ian7aylor/ECE411Practicum/Logistics/Project_Preliminaries/Practicum_Project_Ideas.pdf

# Practicum

## Top Three Project Ideas

Portland State University

Maseeh College of Engineering & Computer Science

Department of Electrical & Computer Engineering

### Authors:

Nick Long

Marcus Chalona

Ali Saad

Ian Taylor

### October 12, 2019


ECE 411

Industry Design Processes

Lab 1 Report | PSU ECE 411

## Contents

1 Project Ideas | 2

1.3 Project Idea #3 - Dancing Lights (Sound Frequency to LED Visualizer) 4

2 Conclusion | 5
1900 SW 4th Ave,, Portland, OR 97201 • https://github.com/ECE411Practicum (https://github.com/ian7aylor/ECE411Practicum/) | 1

## 1 Project Ideas

### 1.1 Project Idea #1 - HVAC Controlled Fan for a Server

### Room

Description: A temperature sensor will take in temperature values and delivers this information to a microcontroller. This microcontroller will then use arithmetic to determine the amount of voltage that will go on the output. This output voltage will drive a fan.

Sensor: Temperature Sensor
Controller: ATMega32U4-AU
Actuator: Fan
1900 SW 4th Ave,, Portland, OR 97201 • https://github.com/ECE411Practicum (https://github.com/ian7aylor/ECE411Practicum/) | 2

### 1.2 Project Idea #2 - Solar Light Sensor

Description: A solar panel will induce current and charge a battery. The controller will check voltage values from the previous 15 minutes to determine whether or not to start a motor that will change the angle of the solar panel(s) to find the next optimal position.

Sensor: Solar Array
Controller: ATMega32U4-AU
Actuator: Motor for realignment of solar panel(s)
1900 SW 4th Ave,, Portland, OR 97201 • https://github.com/ECE411Practicum (https://github.com/ian7aylor/ECE411Practicum/) | 3

### 1.3 Project Idea #3 - Dancing Lights (Sound Frequency to

### LED Visualizer)

Description: A microphone will be connected to multiple bandpass filters with specific frequency ranges. These filters will be connected to input pins of the ATMega32U4-AU. The ATMega32U4-AU will be programmed to take the voltage input from the bandpass filters and determine which LED strips to light up on the Neopixel LED strip.

Sensor: Microphone
Controller: ATMega32U4-AU
Actuator: Neopixels
1900 SW 4th Ave,, Portland, OR 97201 • https://github.com/ECE411Practicum (https://github.com/ian7aylor/ECE411Practicum/) | 4

## 2 Conclusion

As a group, we have decided that the Dancing Lights (Sound Frequencies to LED Visualization) project will give us the right amount of challenge for a 10 week project. We have equal amount of electrical and computer engineering majors in the group, so it was essential to have both analog and digital components.

1900 SW 4th Ave,, Portland, OR 97201 • https://github.com/ECE411Practicum (https://github.com/ian7aylor/ECE411Practicum/) | 5
