ian7aylor/ECE411Practicum/Logistics/ECE411HW4_ProjectSchedule.pdf

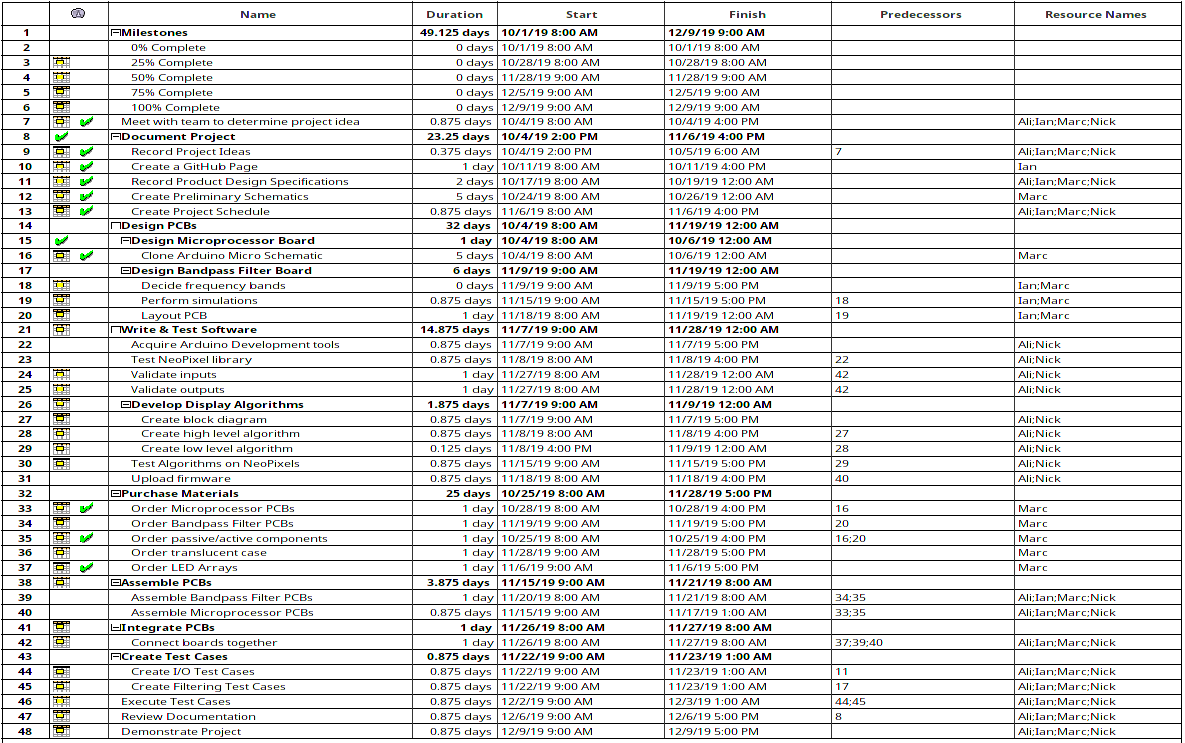
[picture p4: page 1]
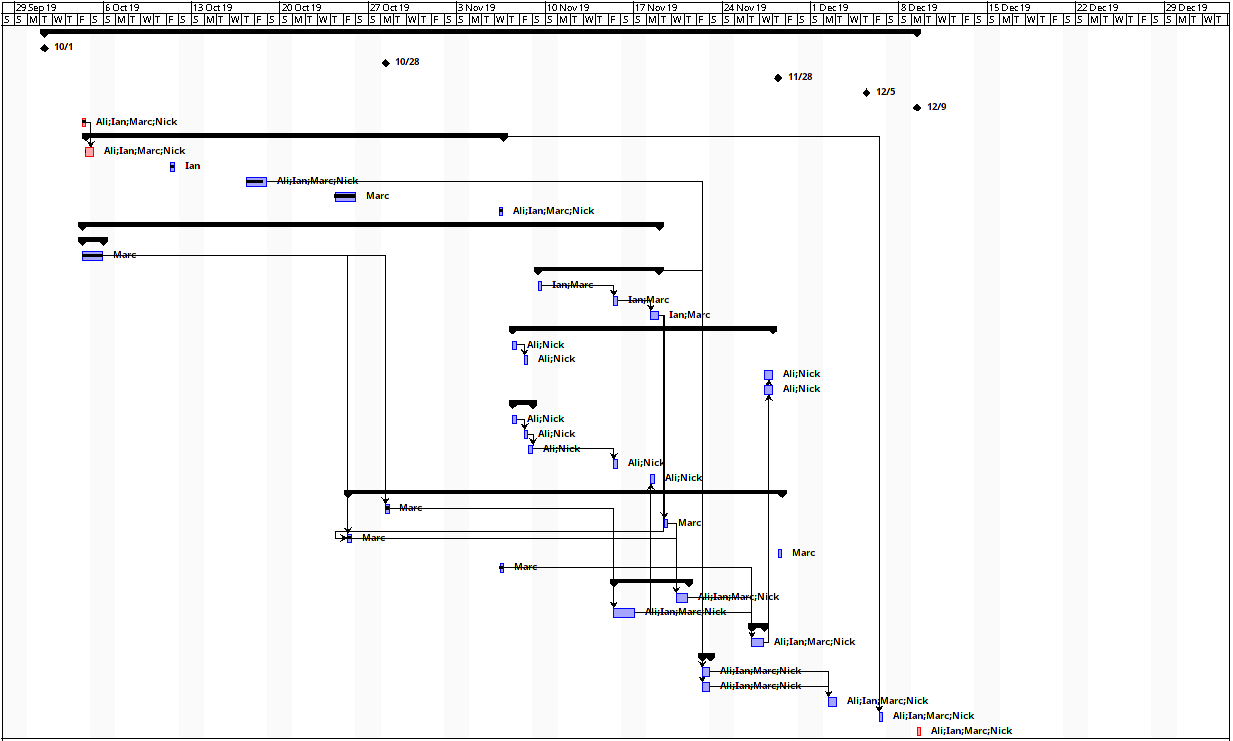
[picture p5: page 2]
