ian7aylor/ECE411Practicum/PCB Design & Layout/Layout/Ver1.2/PCB_Micro-Complete-Ver1.2_20191123182838/2adf127c-40fa-482e-ba70-ac2b44b57d2d.pdf

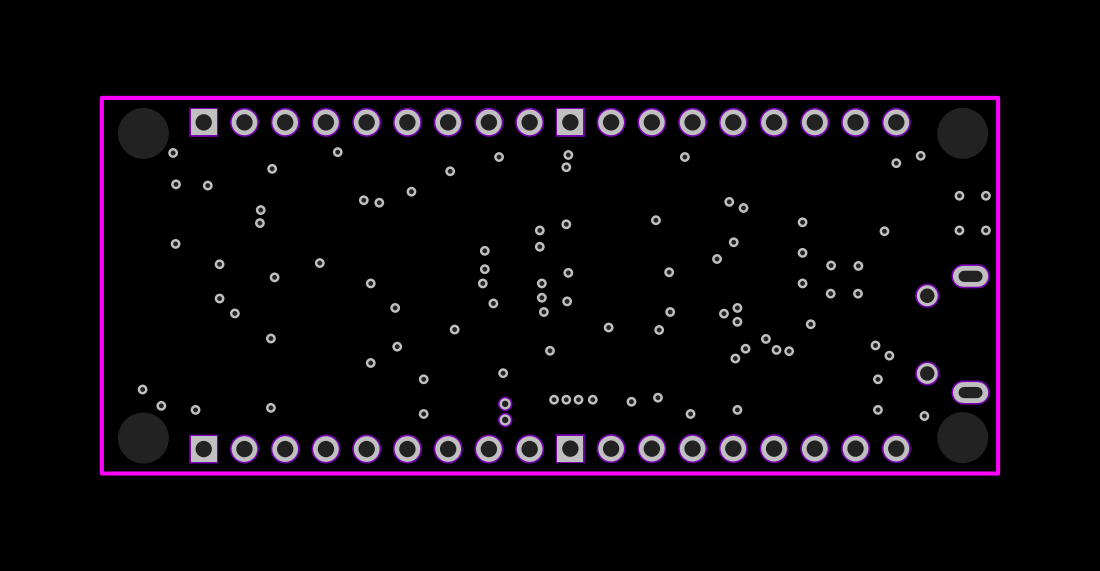
[picture p27: page 1]
