ian7aylor/ECE411Practicum/PCB Design & Layout/Layout/Ver1.2/PCB_Micro-Complete-Ver1.2_20191123182838/3e3d6713-1ce4-48b5-b2b1-c073c7c68c88.pdf

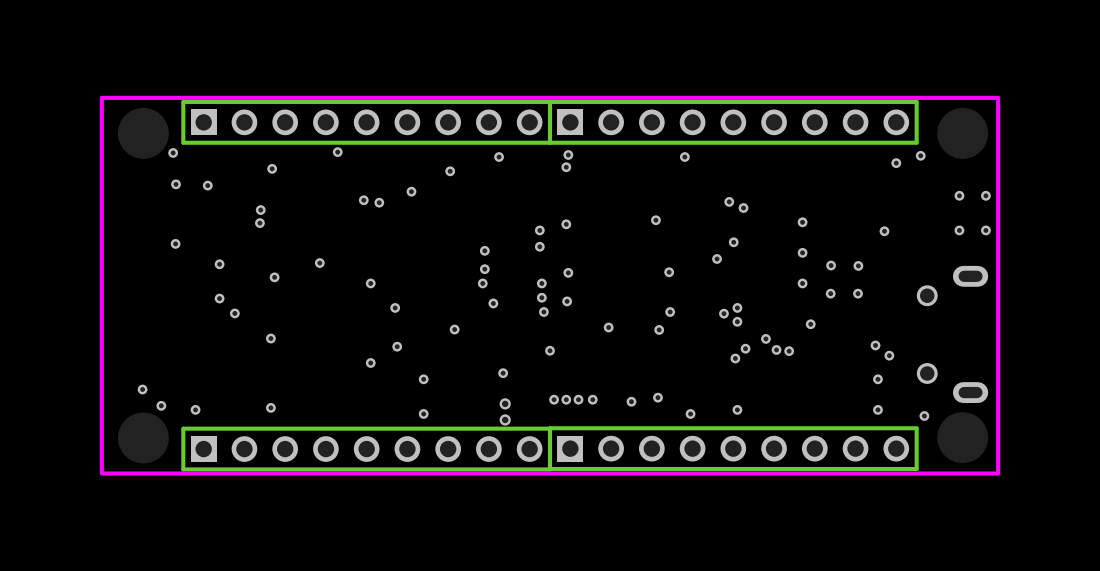
[picture p28: page 1]
