ian7aylor/ECE411Practicum/PCB Design & Layout/Layout/Ver1.2/PCB_Micro-Complete-Ver1.2_20191123182838/42185755-5dae-47f9-ac27-efa17913c4ca.pdf

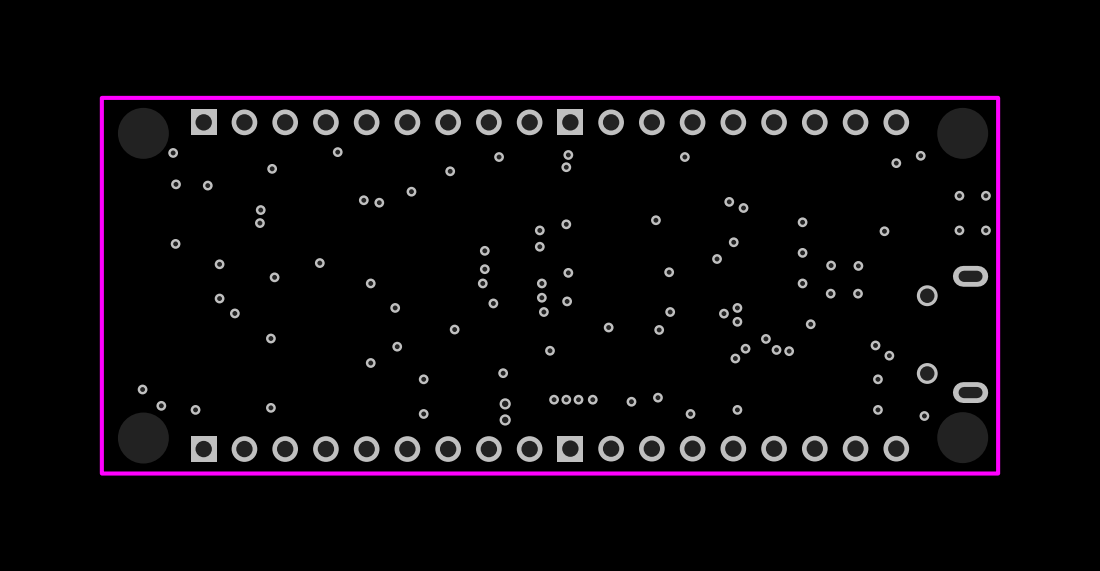
[picture p29: page 1]
