ian7aylor/ECE411Practicum/PCB Design & Layout/Layout/Ver1.2/PCB_Micro-Complete-Ver1.2_20191123182838/78972058-2b17-489f-846a-e816b7262c7a.pdf

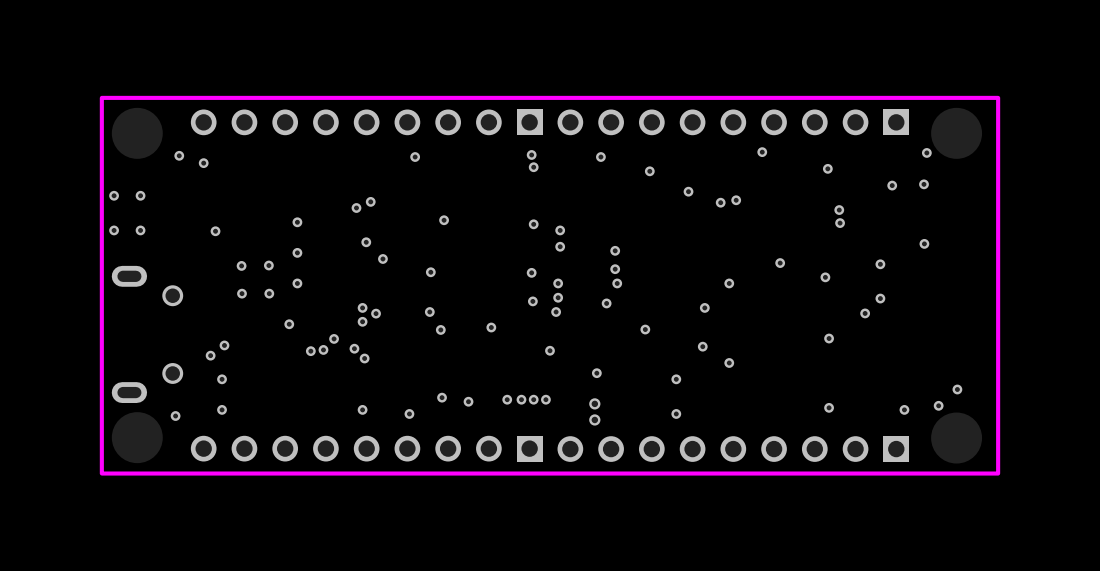
[picture p30: page 1]
