ian7aylor/ECE411Practicum/PCB Design & Layout/Layout/Ver1.2/PCB_Micro-Complete-Ver1.2_20191123182838/7be0d5c9-0151-4e07-a698-6b192da0d526.pdf

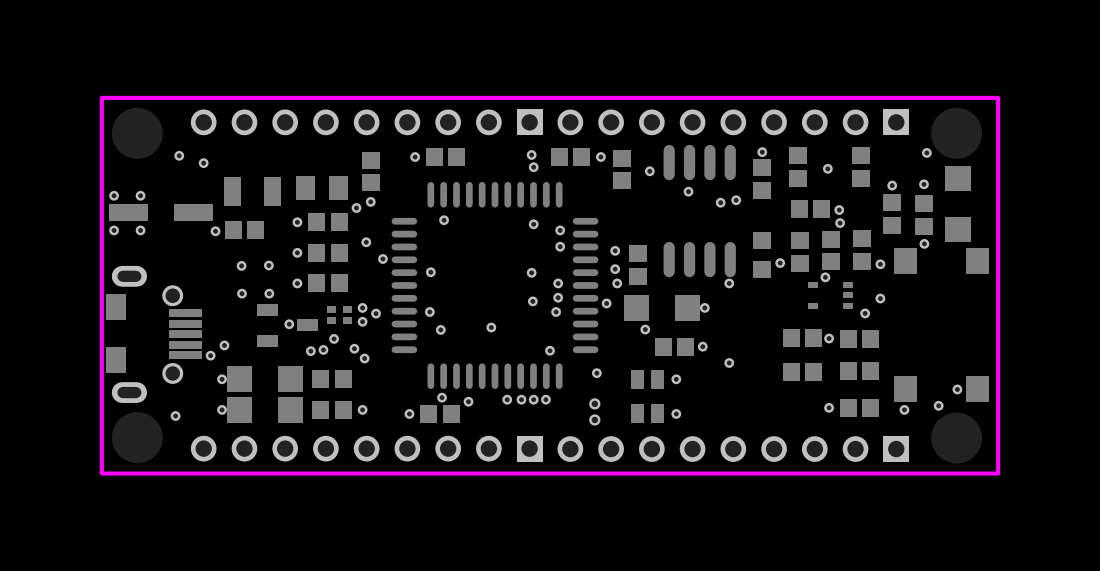
[picture p31: page 1]
