ian7aylor/ECE411Practicum/PCB Design & Layout/Layout/Ver1.2/PCB_Micro-Complete-Ver1.2_20191123182838/7daf5881-57eb-4031-89fc-7f53fe63a61d.pdf

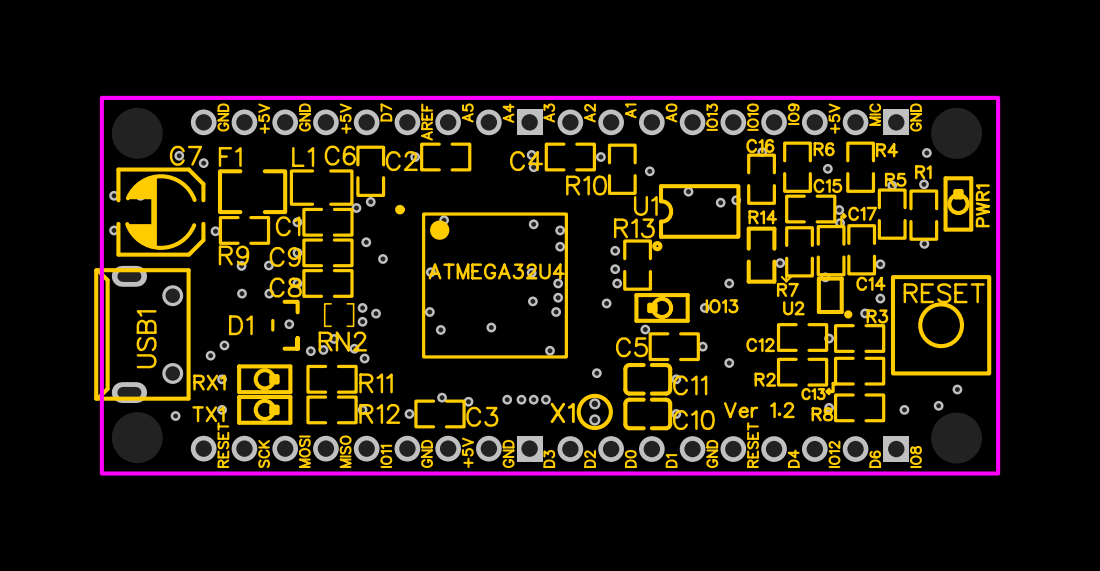
[picture p32: page 1]
