ian7aylor/ECE411Practicum/PCB Design & Layout/Layout/Ver1.2/PCB_Micro-Complete-Ver1.2_20191123182838/902dd1ad-2829-45e7-b100-44baf6f26a92.pdf

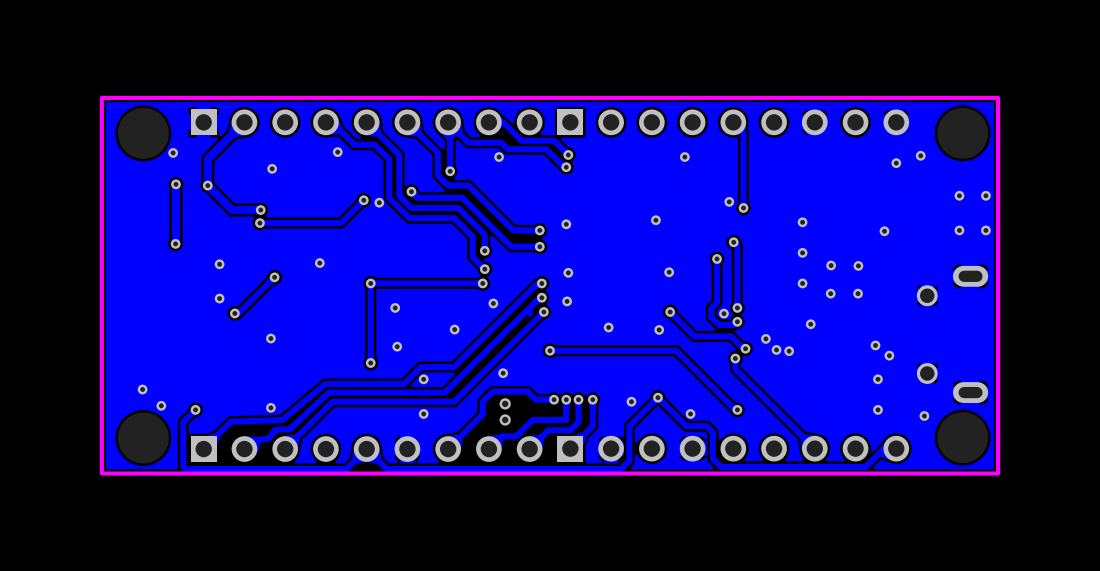
[picture p33: page 1]
