ian7aylor/ECE411Practicum/PCB Design & Layout/Layout/Ver1.2/PCB_Micro-Complete-Ver1.2_20191123182838/e6dc7ab0-4b18-48ef-a373-c5064e3a3ff5.pdf

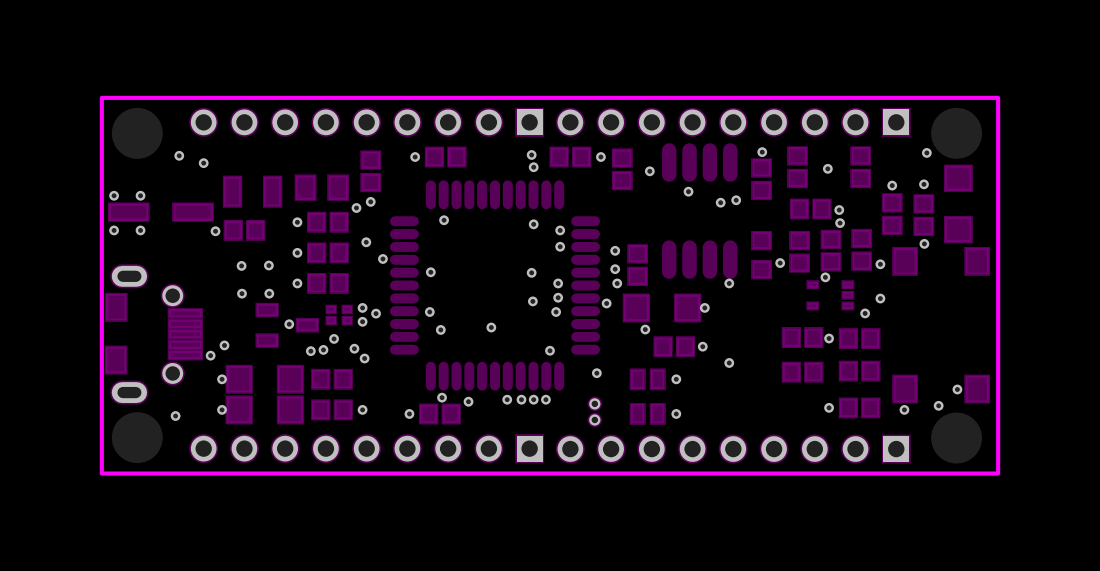
[picture p34: page 1]
