ian7aylor/ECE411Practicum/PCB Design & Layout/Layout/Ver1.2/PCB_Micro-Complete-Ver1.2_20191123183032/0f5fbee5-654c-4553-b34e-9a6330f1ae8d.pdf

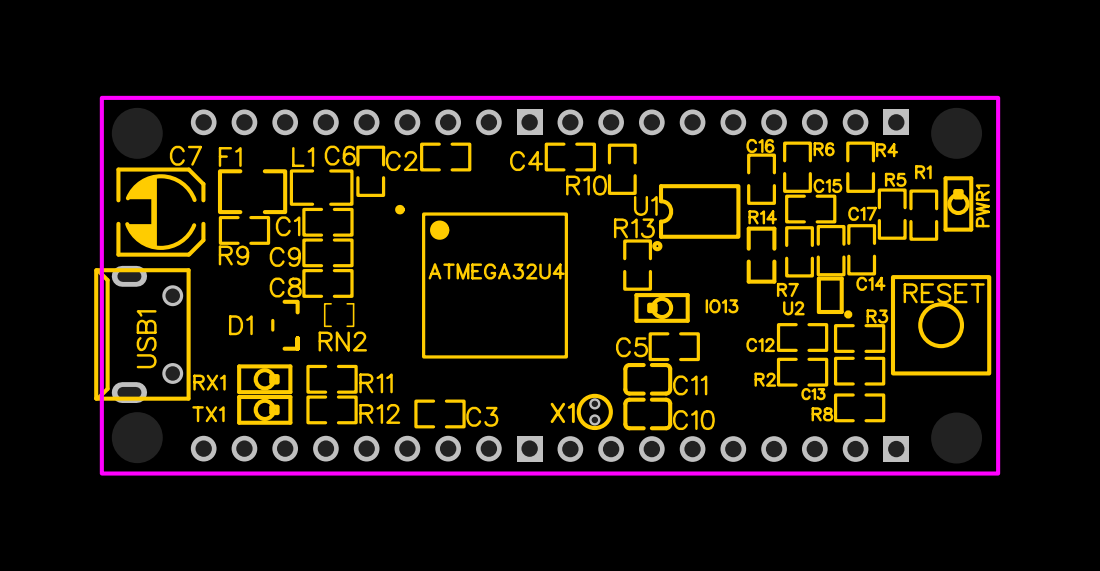
[picture p35: page 1]
