ian7aylor/ECE411Practicum/PCB Design & Layout/Layout/Ver1.2/PCB_Micro-Complete-Ver1.2_20191123183032/14120e1c-3400-4aa1-8a03-b37c3c2f251e.pdf

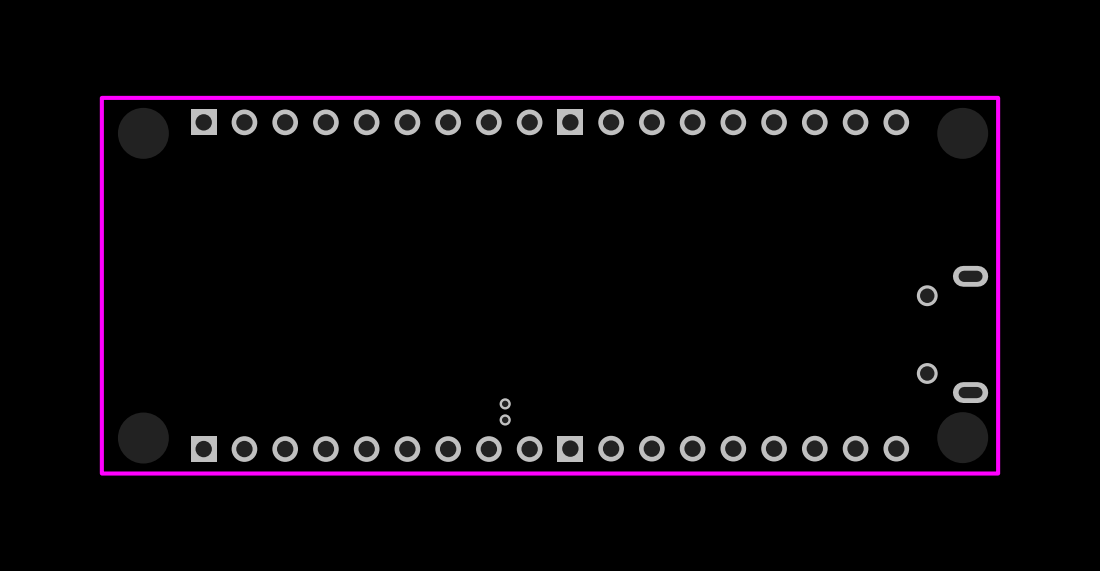
[picture p36: page 1]
