ian7aylor/ECE411Practicum/PCB Design & Layout/Layout/Ver1.2/PCB_Micro-Complete-Ver1.2_20191123183032/2fd0ea34-d89d-4401-8a14-ce33425fee76.pdf

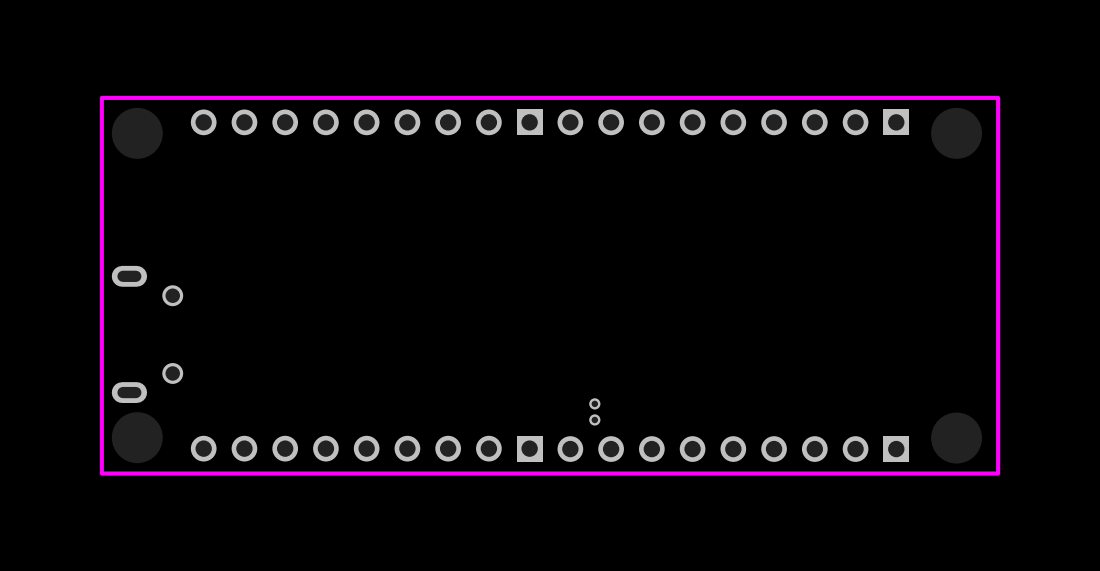
[picture p37: page 1]
