ian7aylor/ECE411Practicum/PCB Design & Layout/Layout/Ver1.2/PCB_Micro-Complete-Ver1.2_20191123183032/3119c9f1-c6d6-4f14-a6e9-f40058ee00e6.pdf

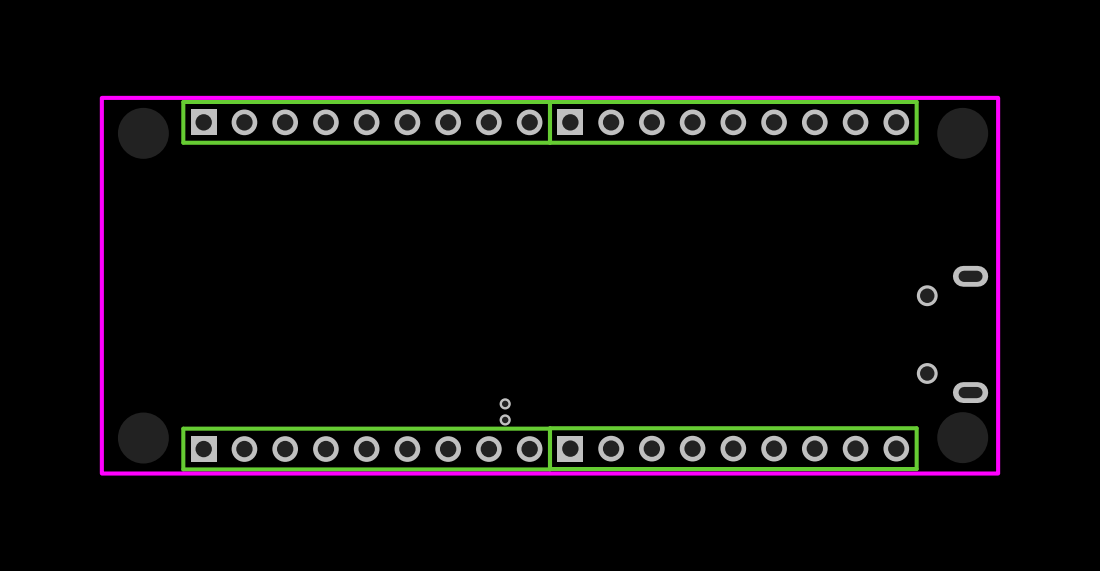
[picture p38: page 1]
