ian7aylor/ECE411Practicum/PCB Design & Layout/Layout/Ver1.2/PCB_Micro-Complete-Ver1.2_20191123183032/31f5569c-e1a5-4952-9578-0bfc36f0eb89.pdf

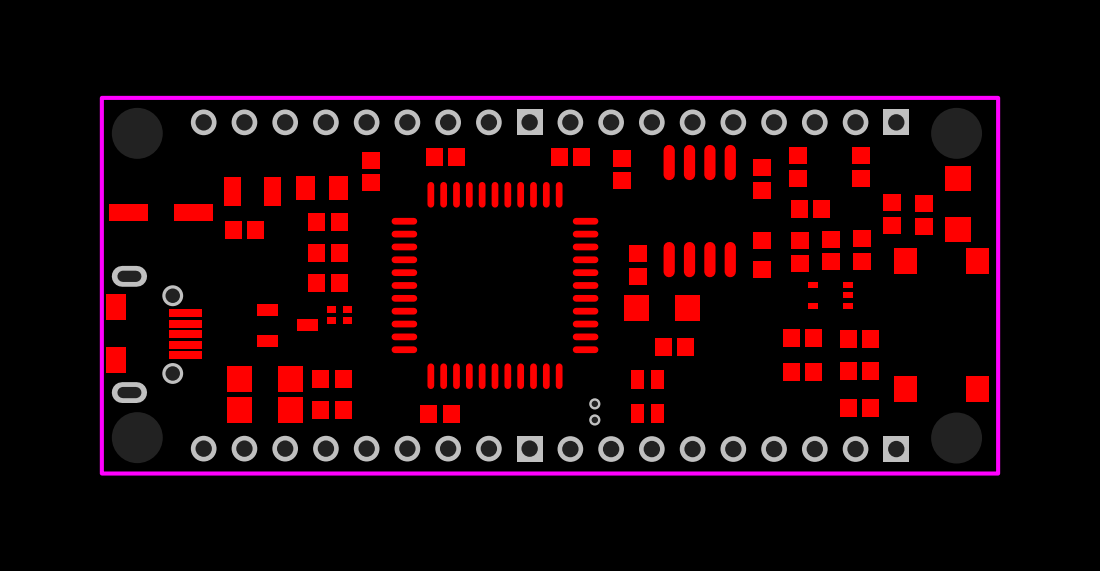
[picture p39: page 1]
