ian7aylor/ECE411Practicum/PCB Design & Layout/VER1.0/Schematic/Schematic_ECE411_ATMEGA32U4 Micro Ver1.0_20191204032329.pdf

## Analog Reference

+5V Selector | +5V Regulator

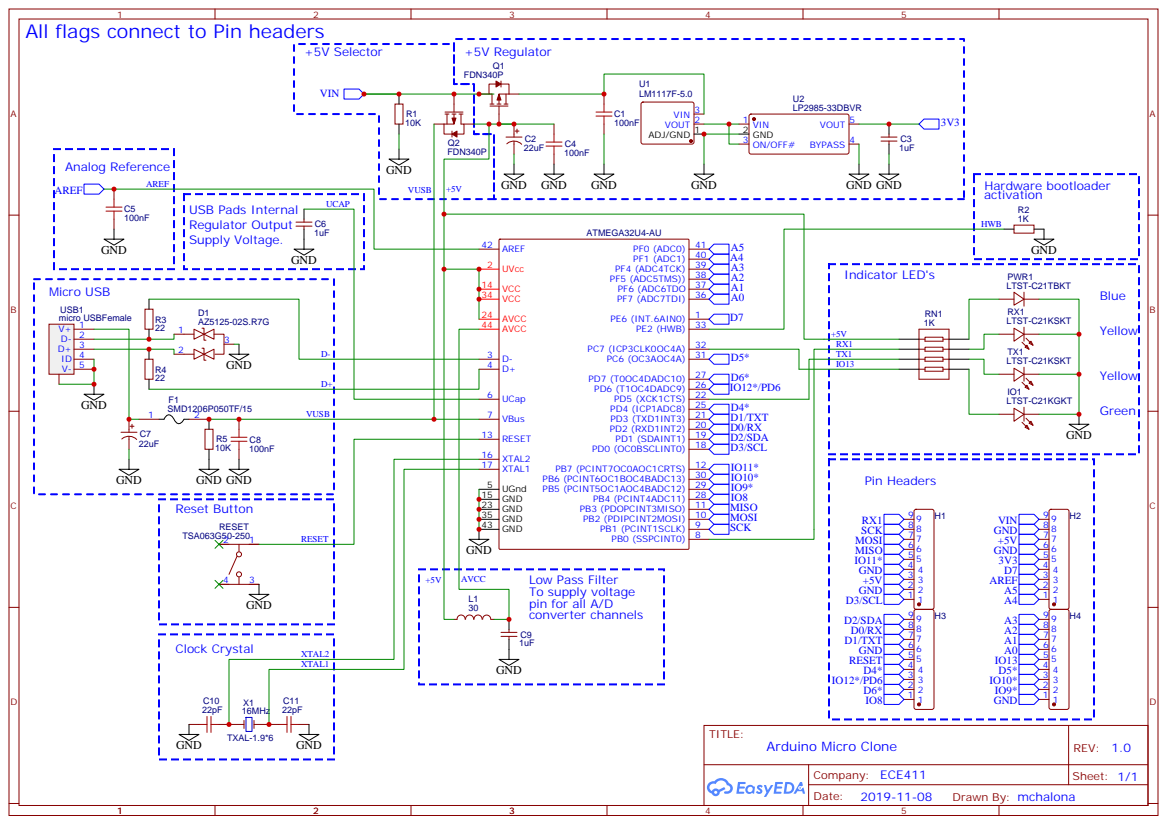
[picture p40: page 1]

All flags connect to Pin headers
