ian7aylor/ECE411Practicum/PCB Design & Layout/VER1.1/Schematic/Schematic_ECE411_ATMEGA32U4 Micro Ver1.1_20191204032943.pdf

## Analog Reference

## USB Pads Internal

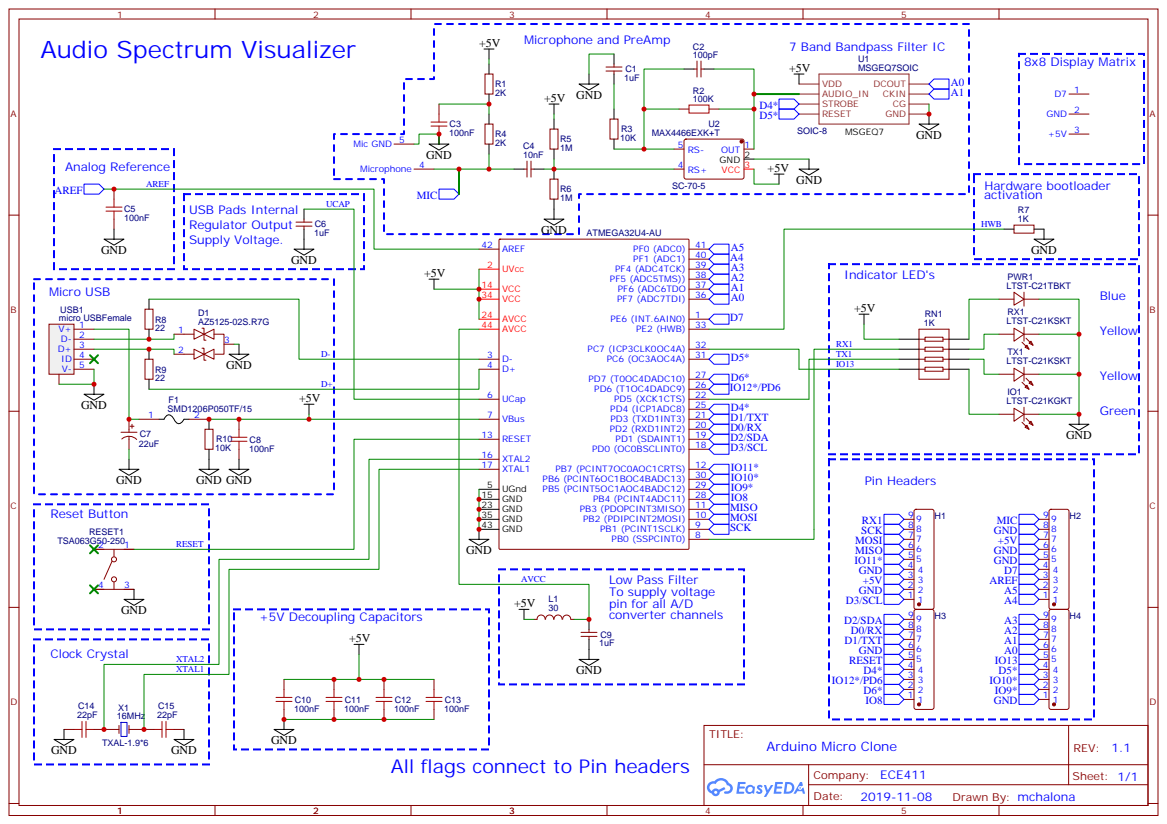
[picture p41: page 1]

7 Band Bandpass Filter IC Microphone and PreAmp

All flags connect to Pin headers
