ian7aylor/ECE411Practicum/PCB Design & Layout/Schematic/Ver1.0/Schematic_Practicum Project ECE411_20191030233733.pdf

## Analog Reference

+5V Selector | +5V Regulator

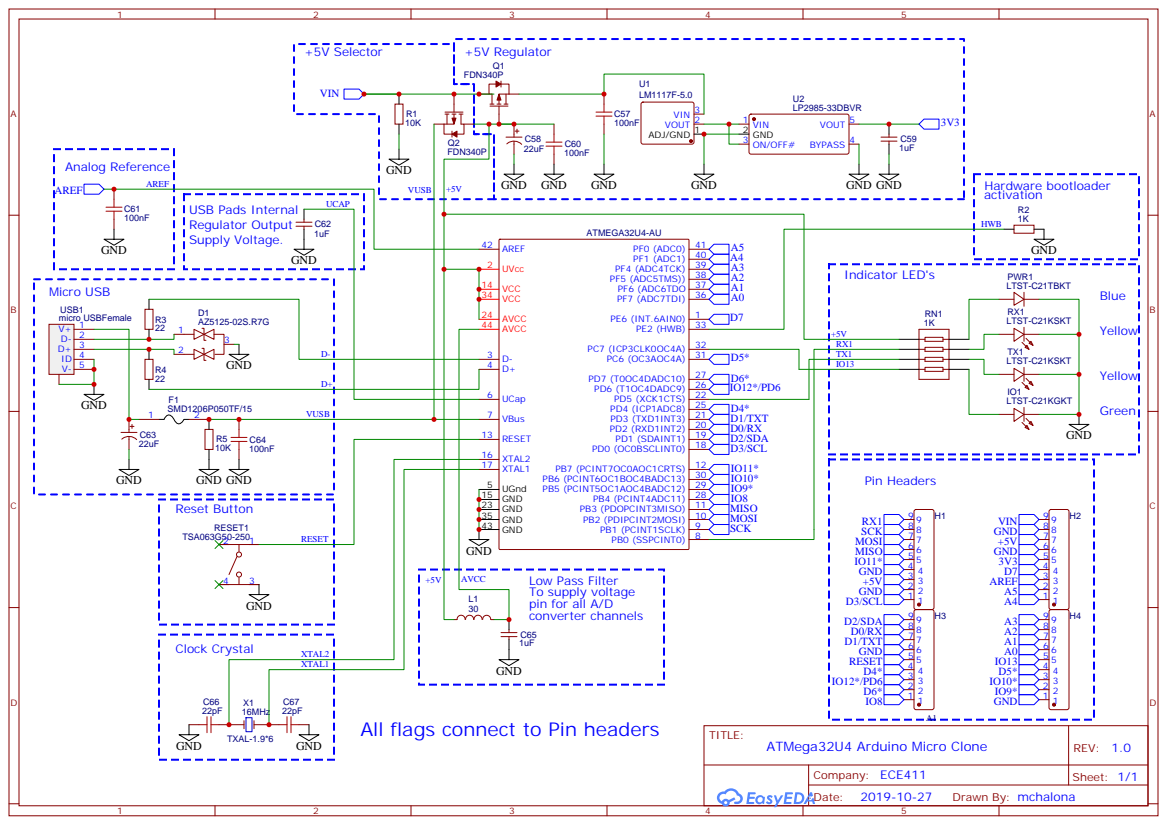
[picture p42: page 1]

All flags connect to Pin headers

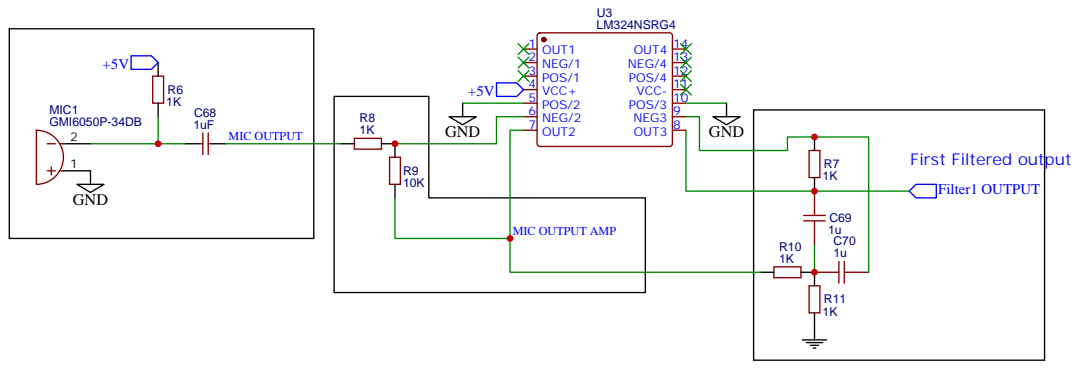
[picture p43: page 2]
