ian7aylor/ECE411Practicum/PCB Design & Layout/VER1.0/PCB Layout/PCB_Micro Complete Ver1.0_20191204032538.pdf

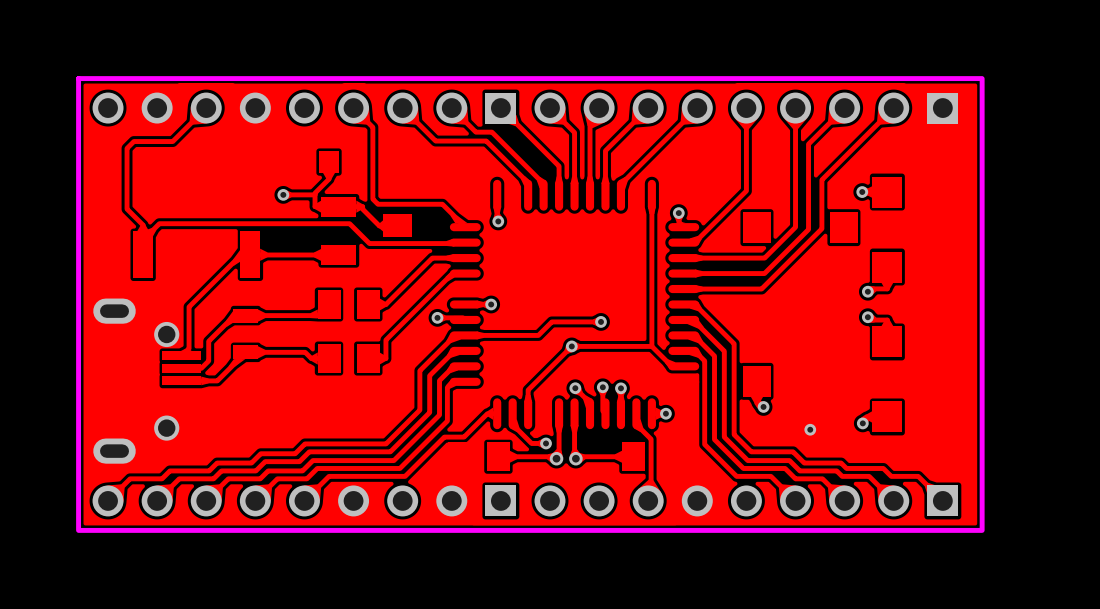
[picture p44: page 1]

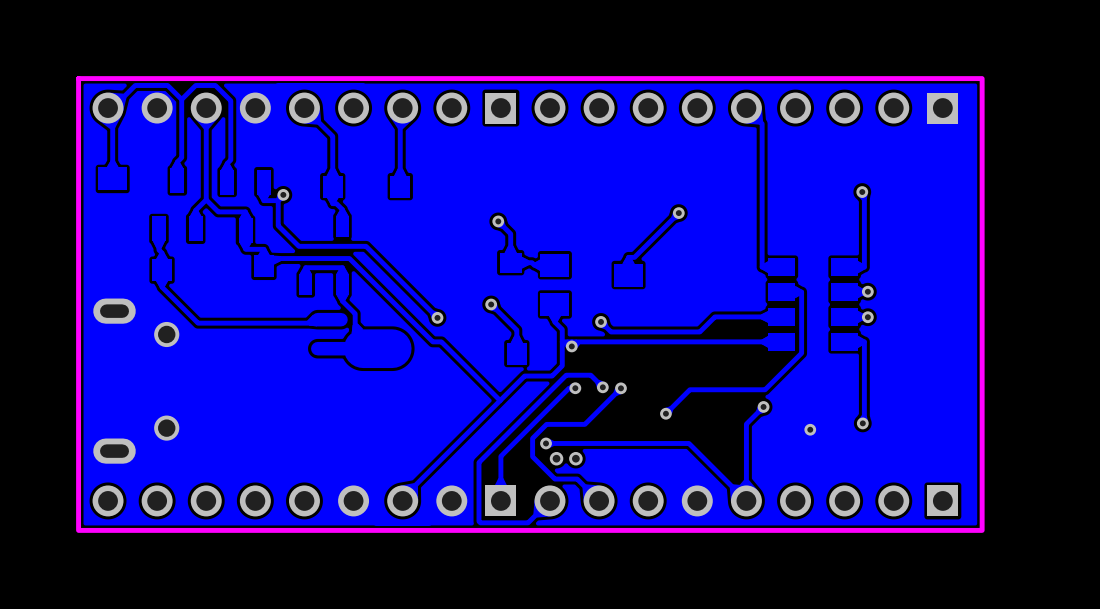
[picture p45: page 2]

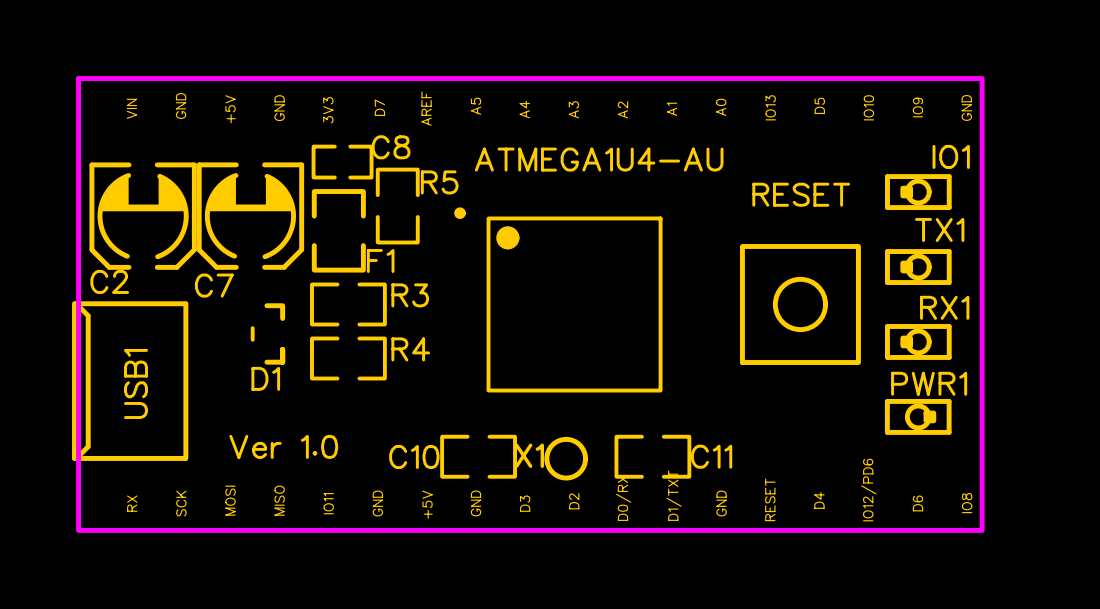
[picture p46: page 3]

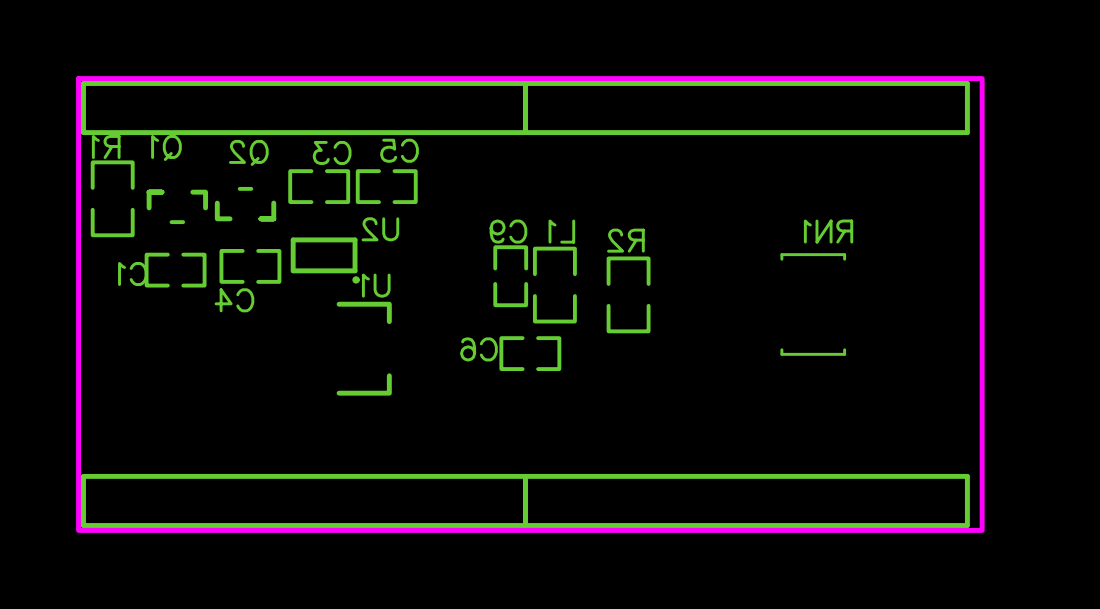
[picture p47: page 4]

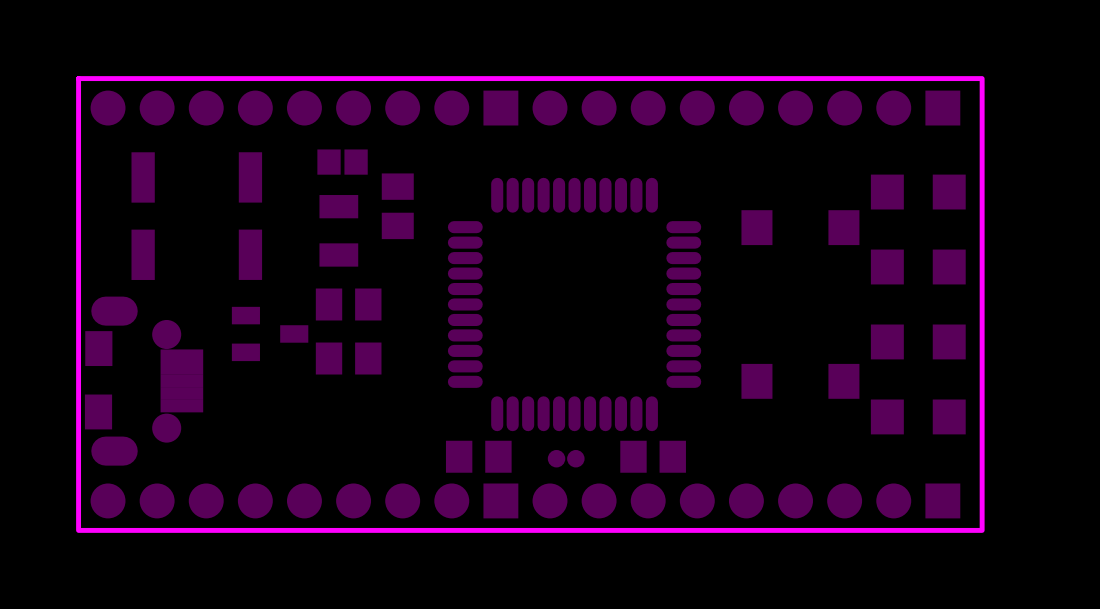
[picture p48: page 7]

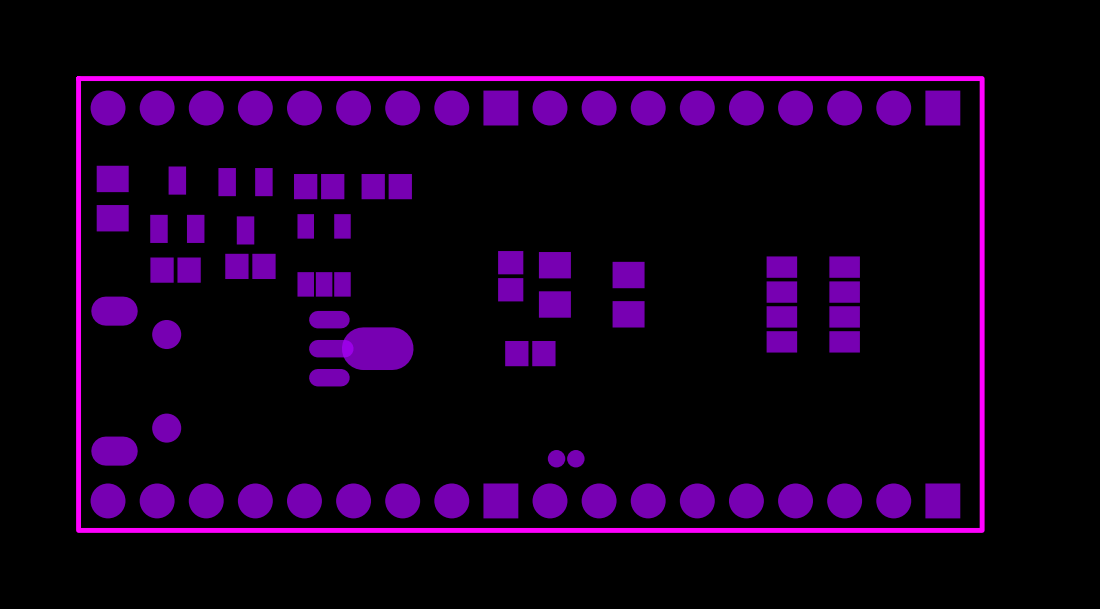
[picture p49: page 8]

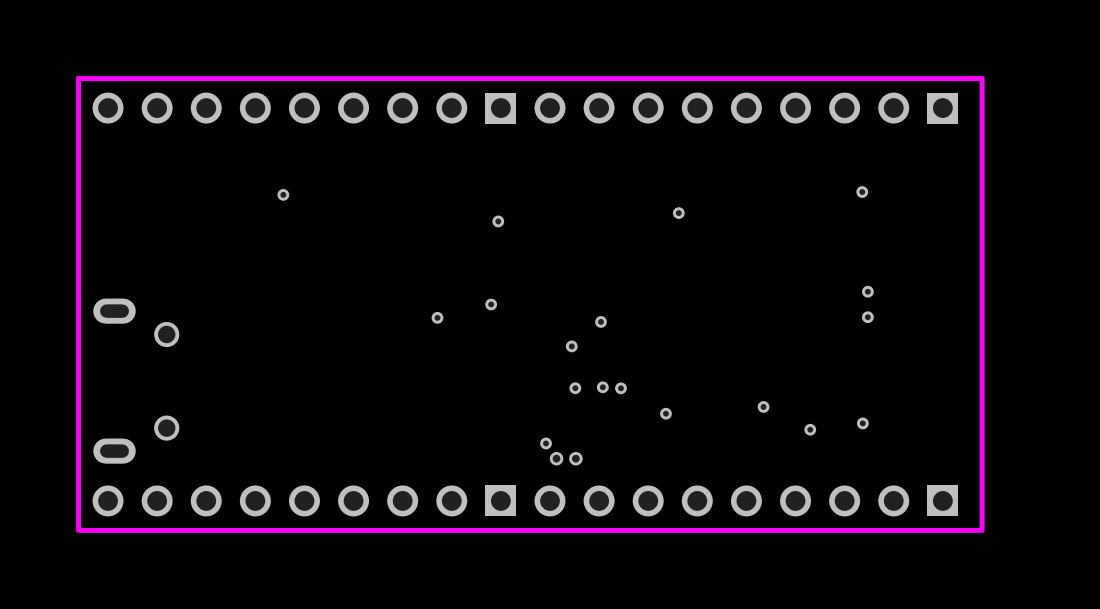
[picture p50: page 10]
