ian7aylor/ECE411Practicum/PCB Design & Layout/VER1.0/PCB Layout/PCB_Micro Complete Ver1.0_20191204032640.pdf

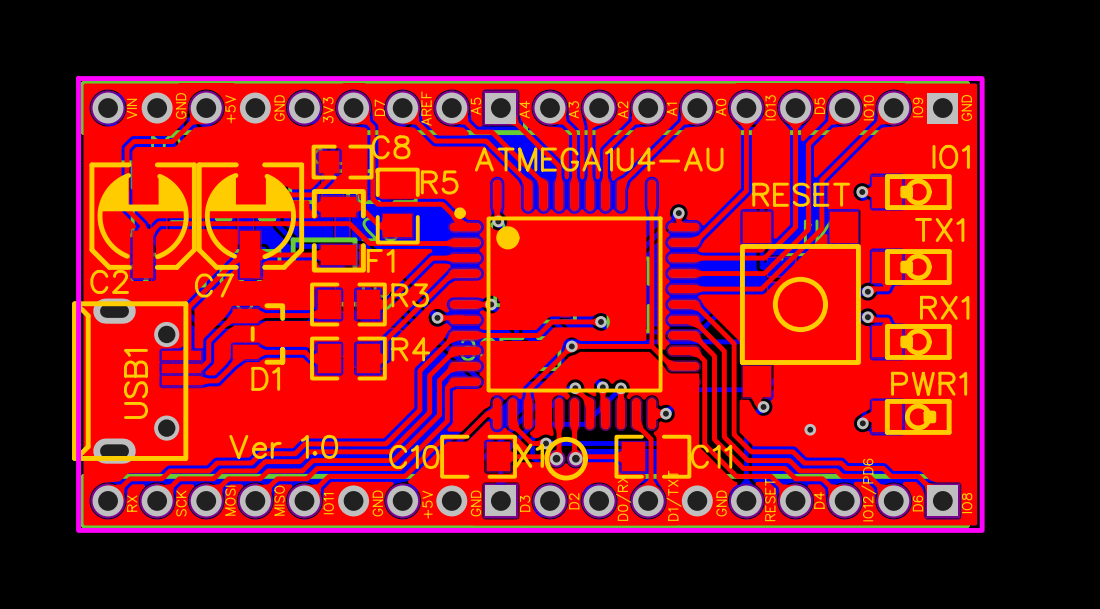
[picture p51: page 1]
