ian7aylor/ECE411Practicum/PCB Design & Layout/VER1.1/PCB Layout/PCB_Micro Complete Ver1.1_20191204033103.pdf

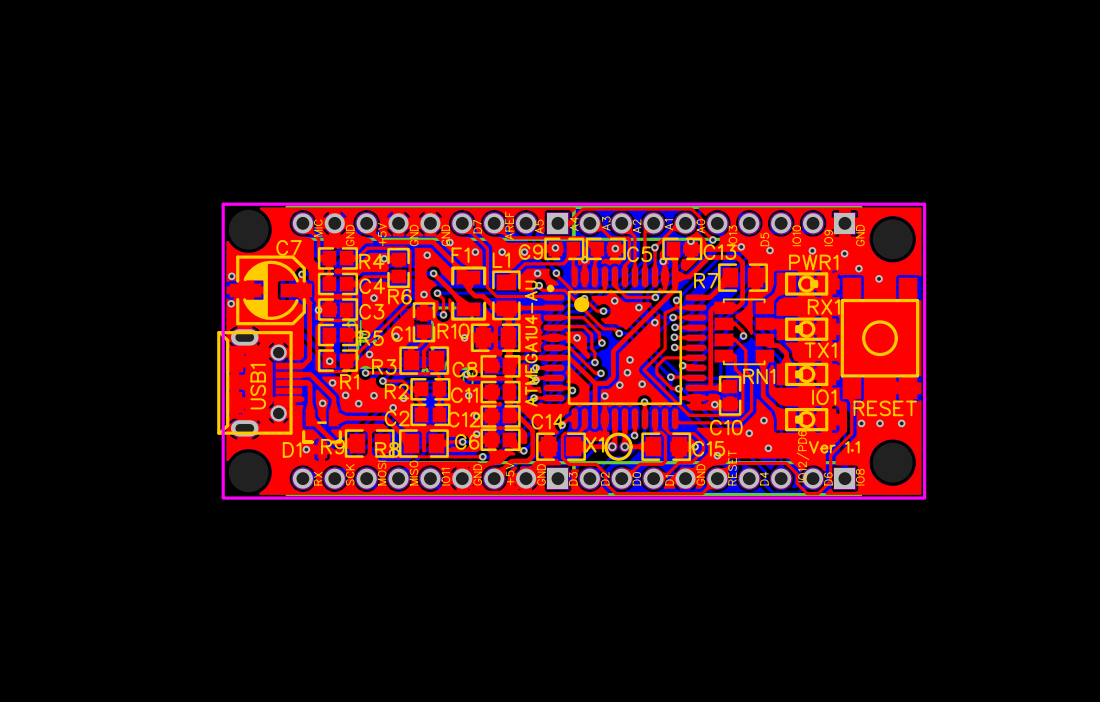
[picture p52: page 1]
