ian7aylor/ECE411Practicum/PCB Design & Layout/VER1.1/PCB Layout/PCB_Micro Complete Ver1.1_20191204033127.pdf

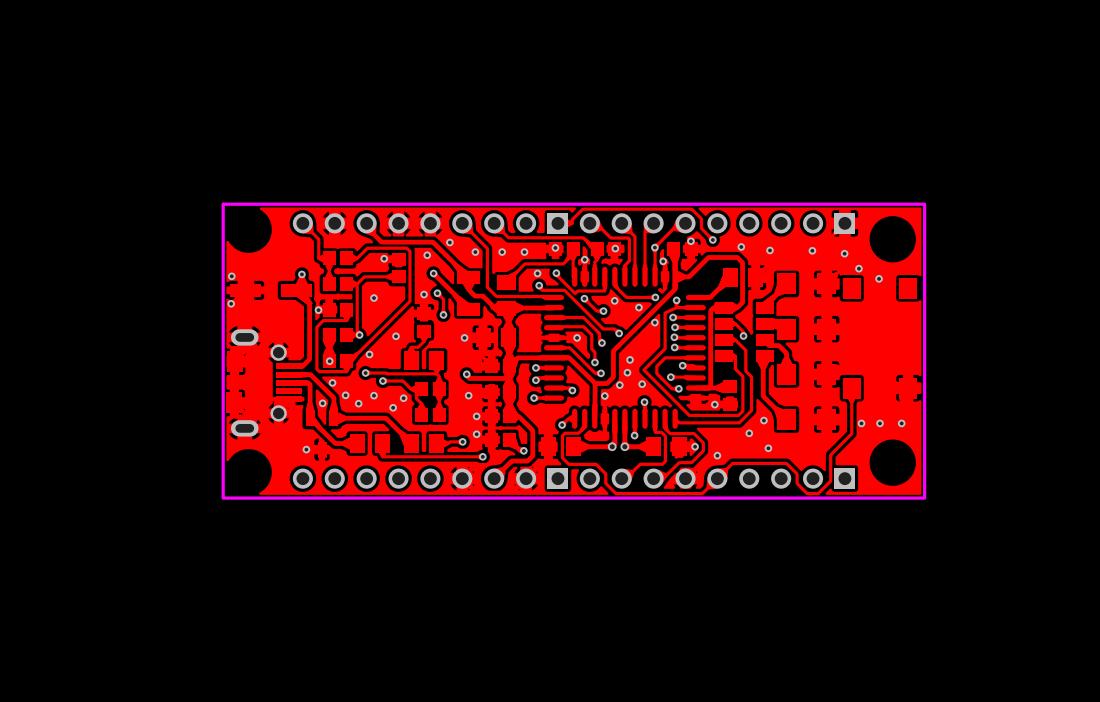
[picture p53: page 1]

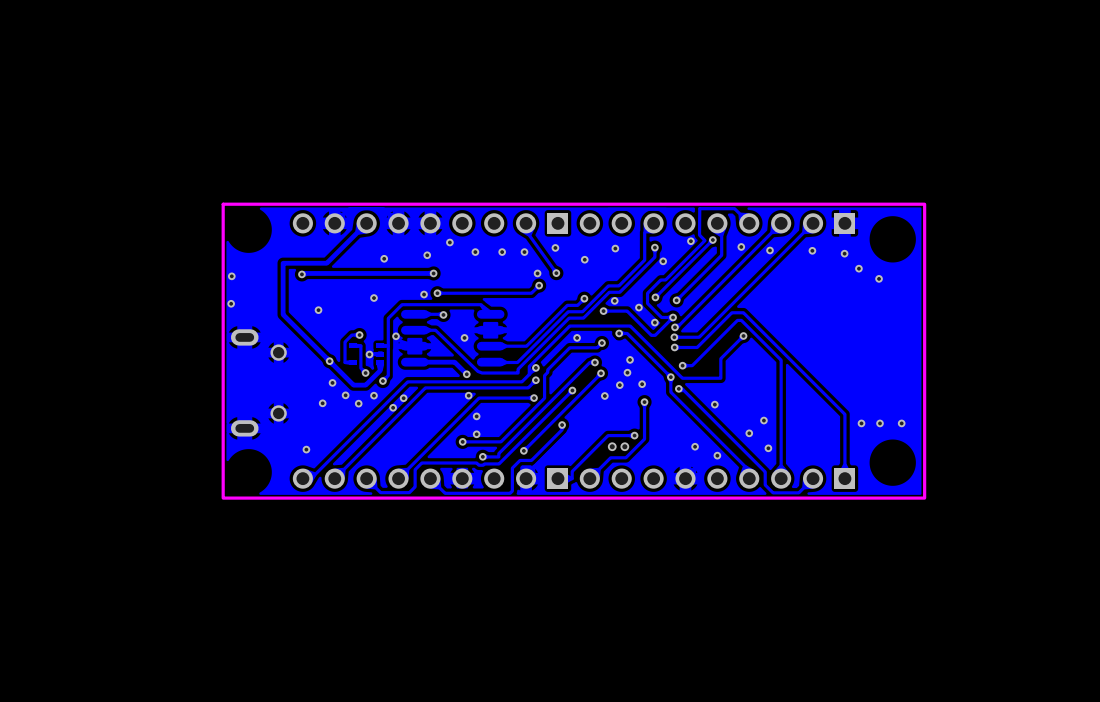
[picture p54: page 2]

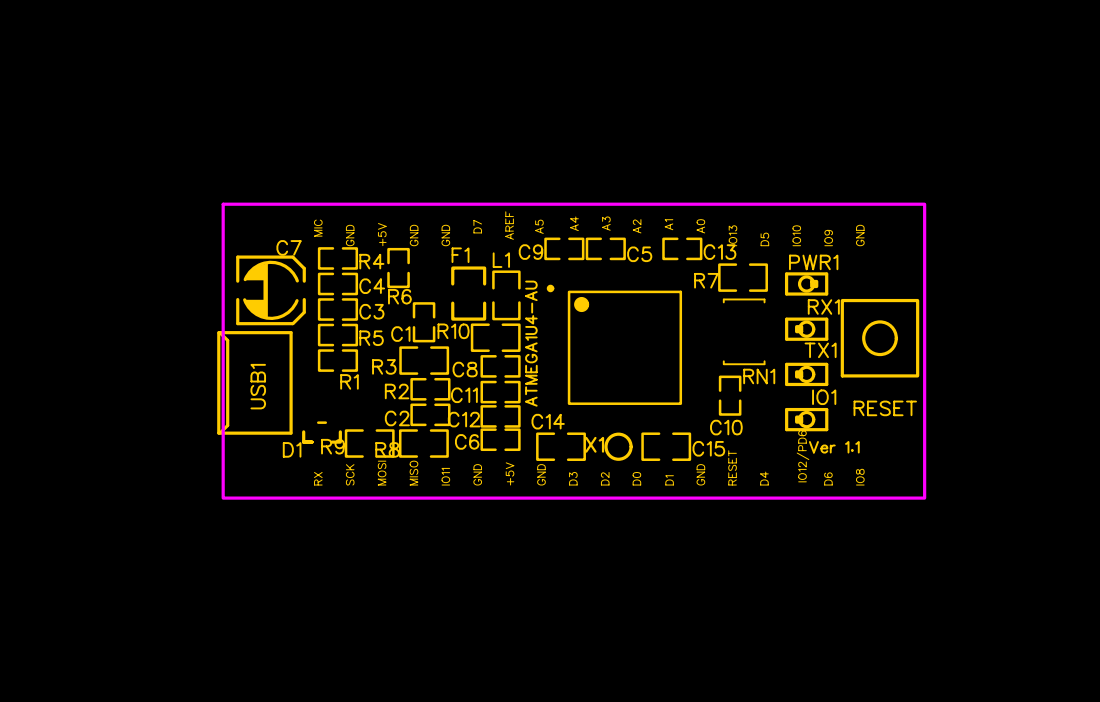
[picture p55: page 3]

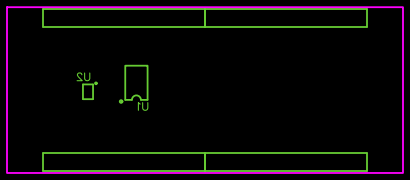
[picture p56: figure]

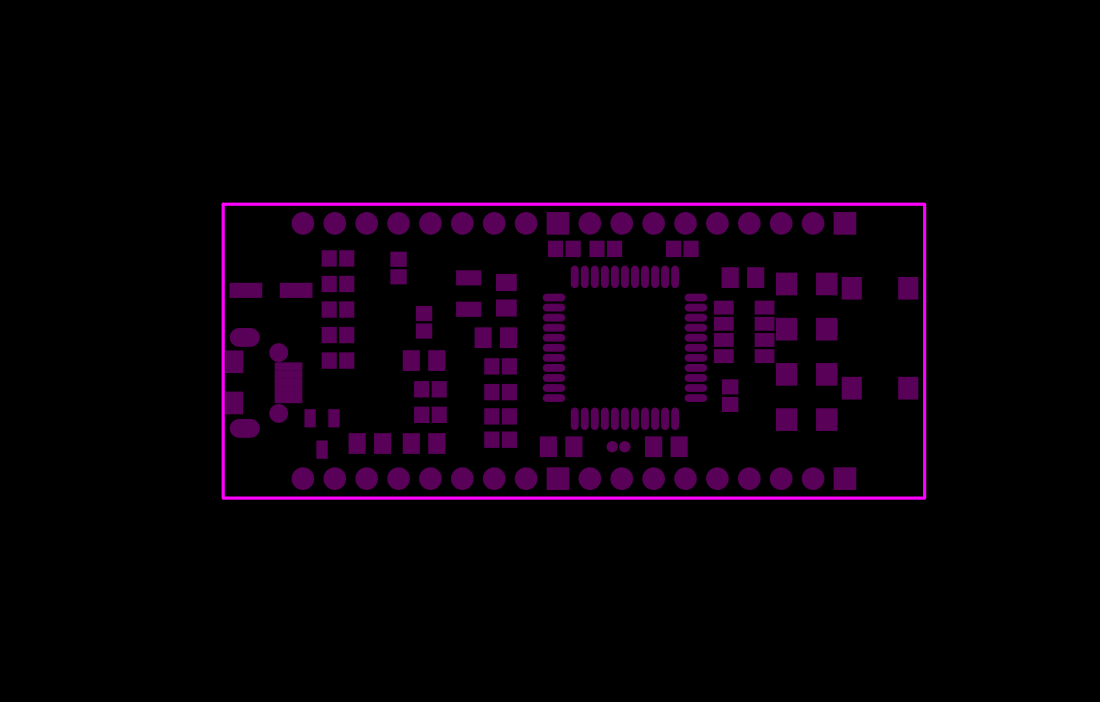
[picture p57: page 7]

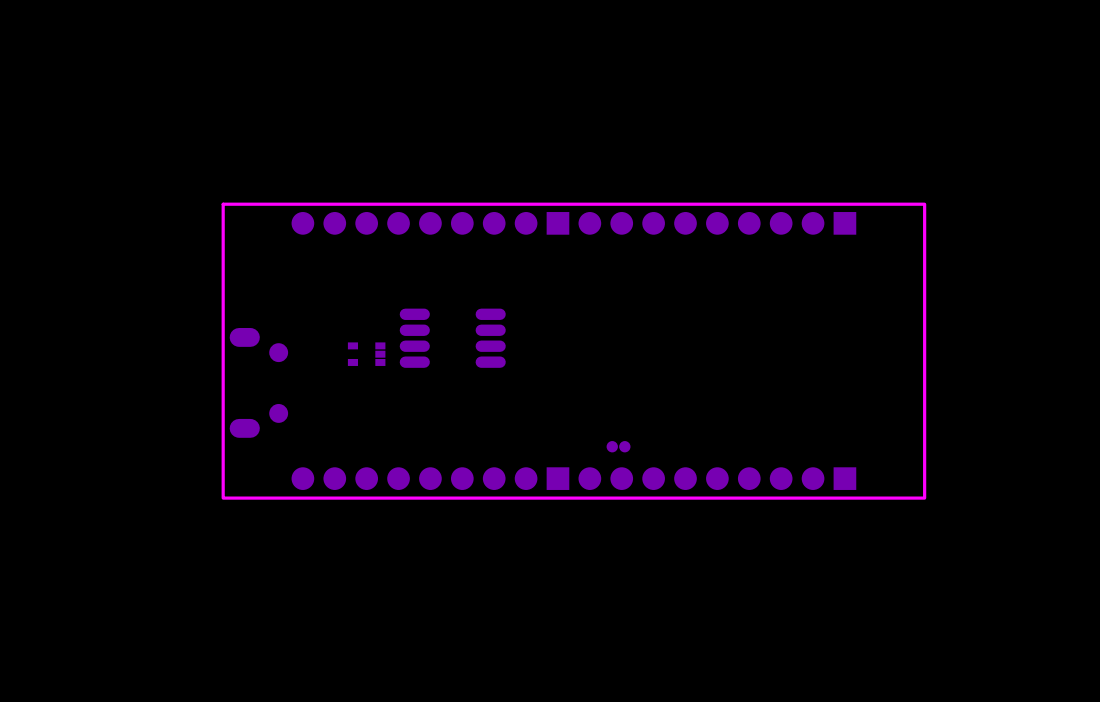
[picture p58: page 8]

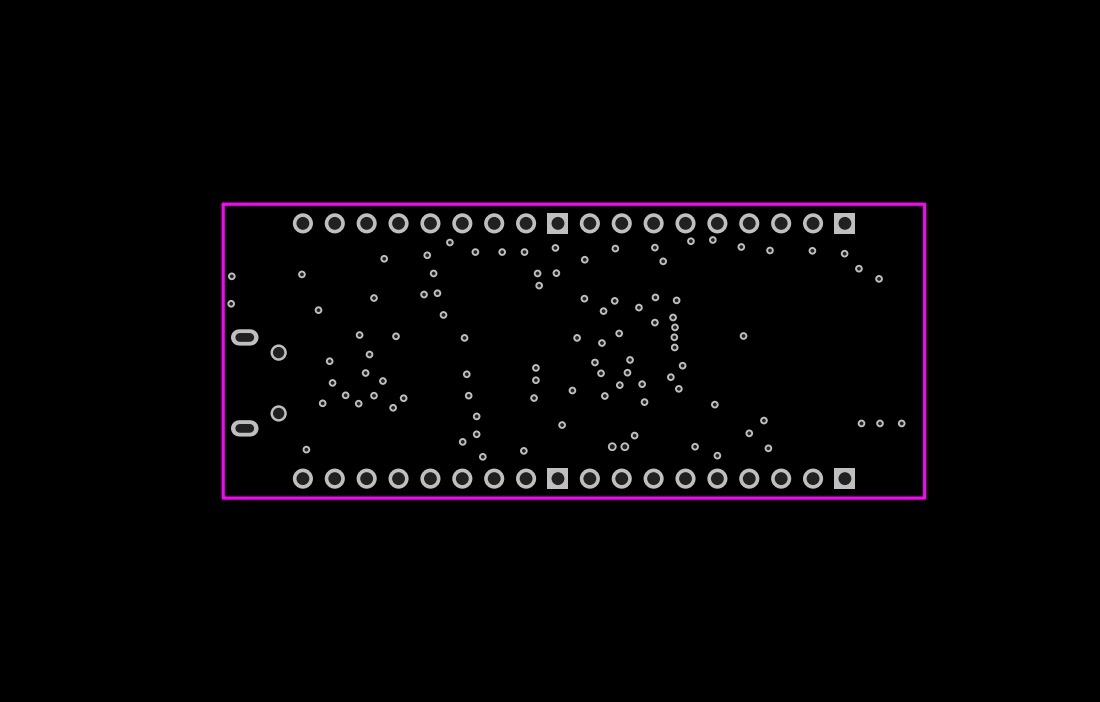
[picture p59: page 10]

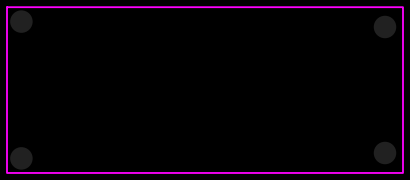
[picture p60: figure]
