ian7aylor/ECE411Practicum/PCB Design & Layout/VER1.2/PCB Layout/PCB_Micro Complete Ver1.2_20191204033536.pdf

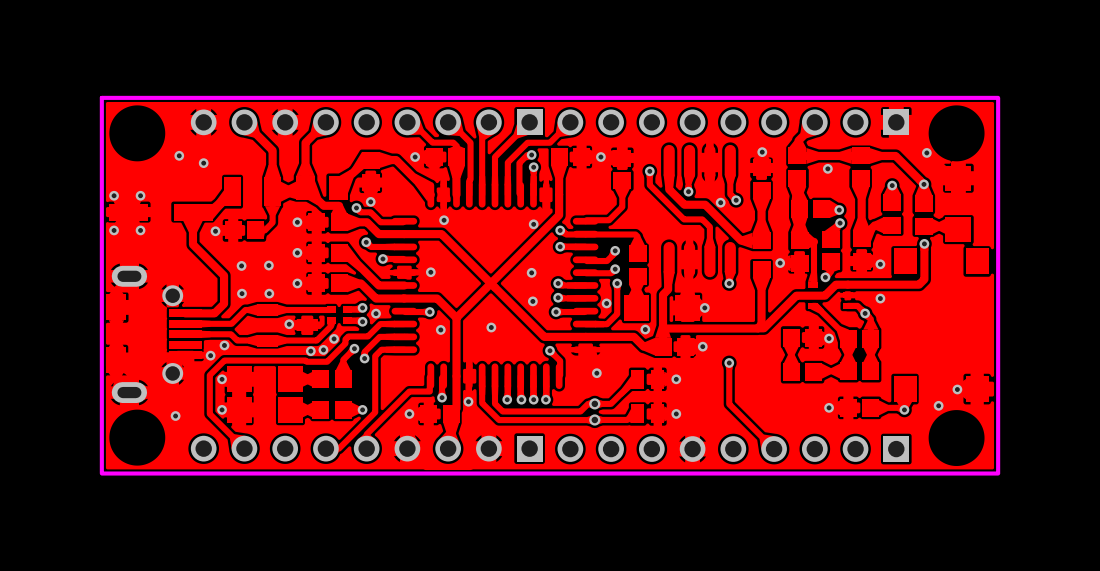
[picture p61: page 1]

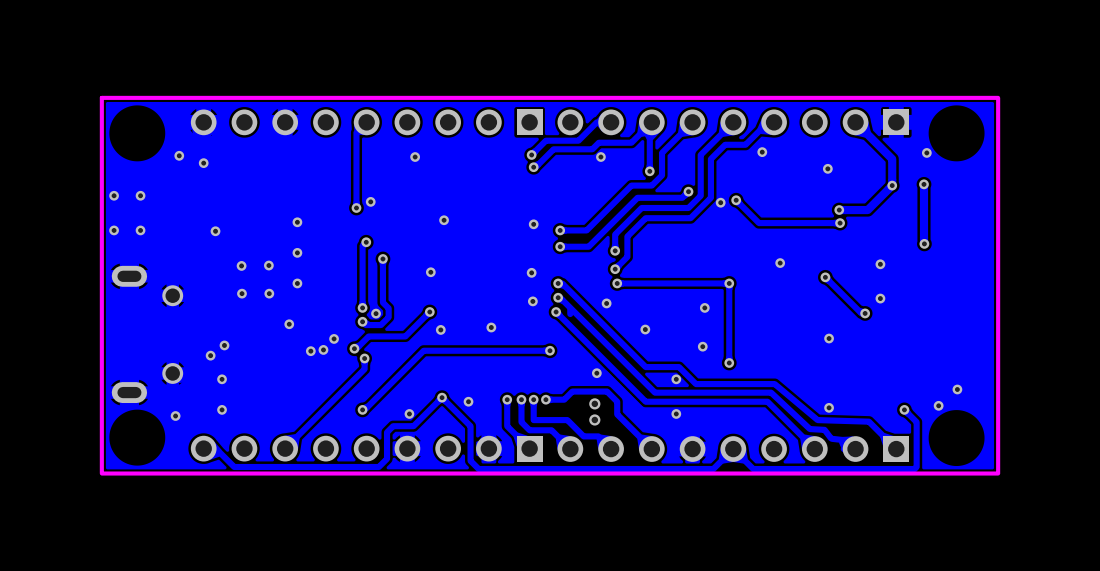
[picture p62: page 2]

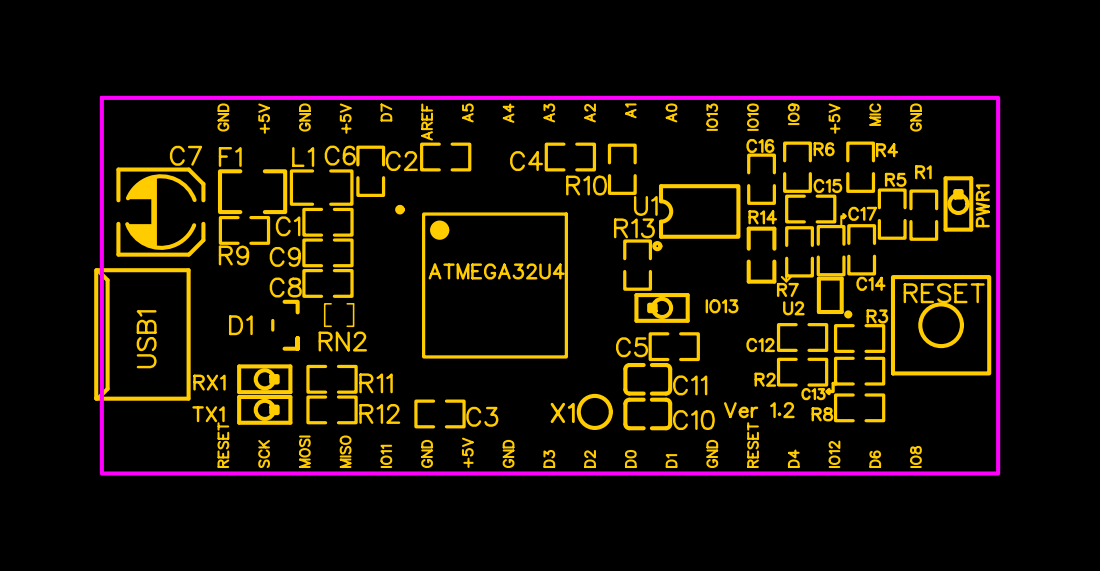
[picture p63: page 3]

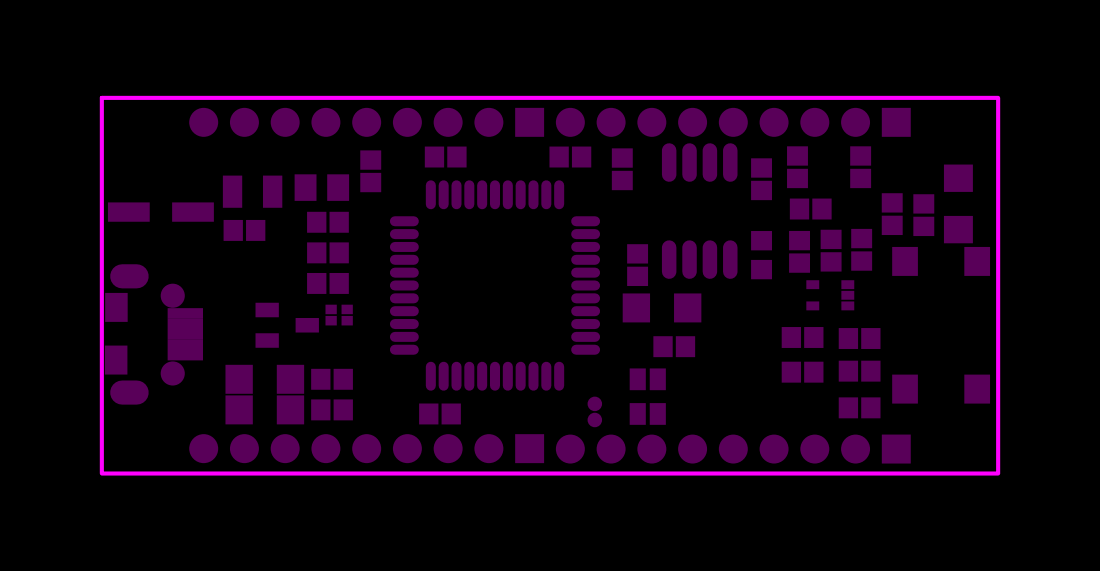
[picture p64: page 7]

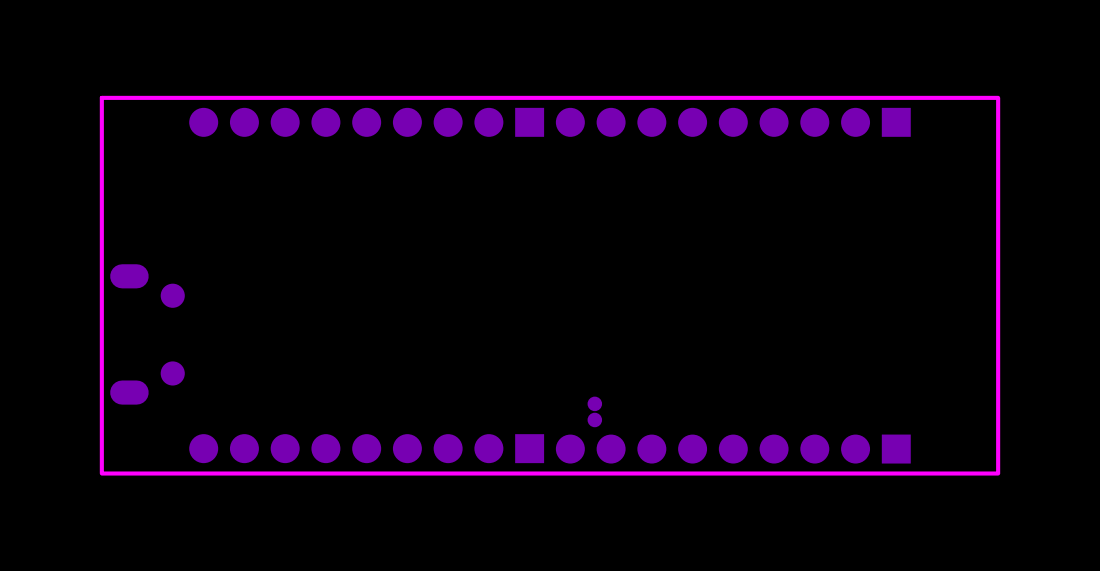
[picture p65: page 8]

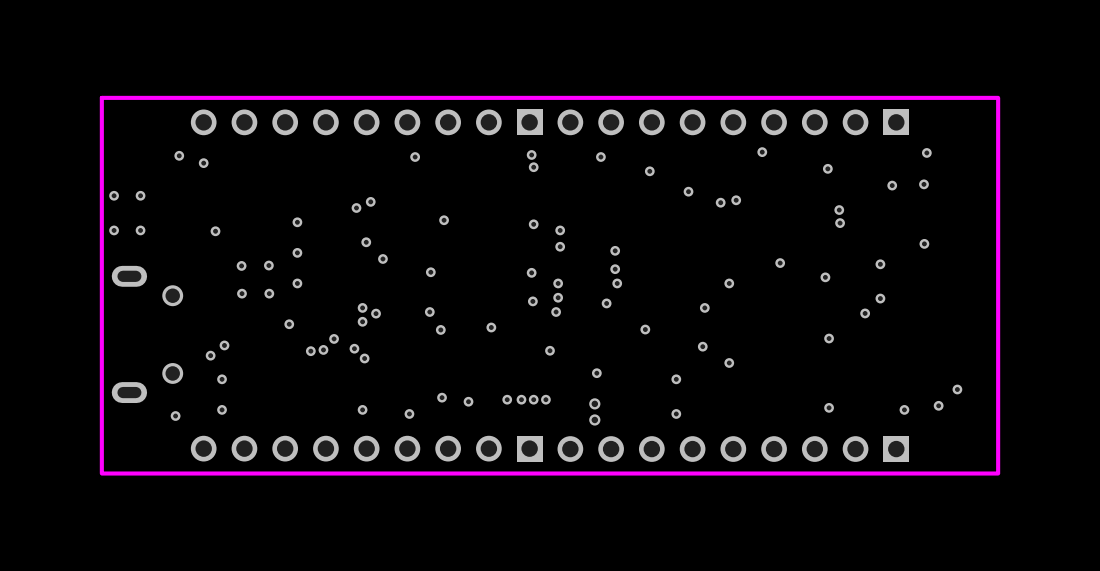
[picture p66: page 10]

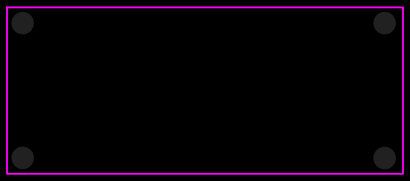
[picture p67: figure]
