ian7aylor/ECE411Practicum/PCB Design & Layout/VER1.2/PCB Layout/PCB_Micro Complete Ver1.2_20191204033604.pdf

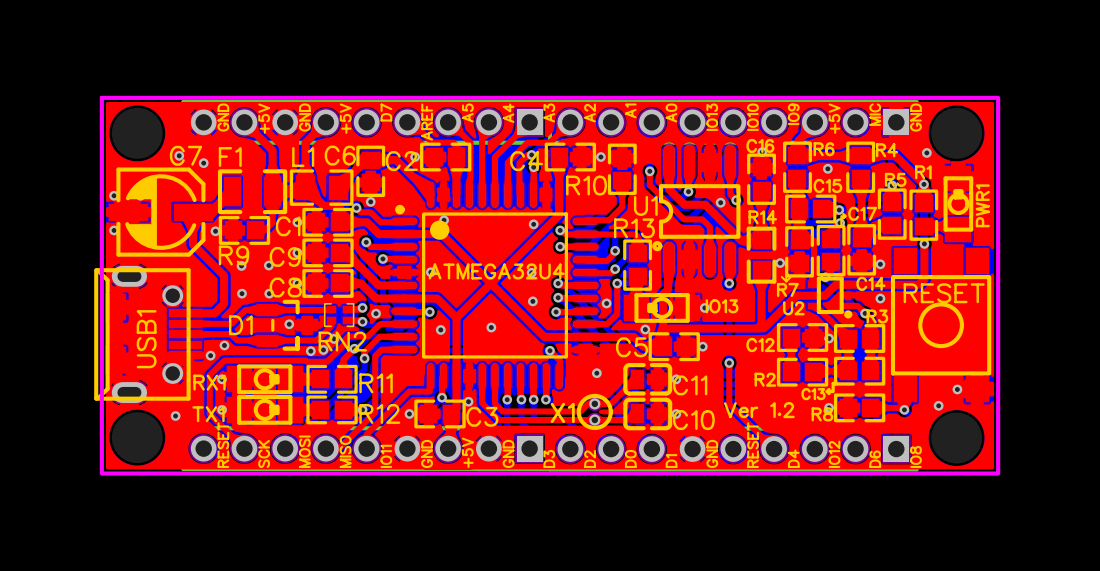
[picture p68: page 1]
